kantholz44mm/led_watch/software/src/core/reset.c

extern int main(void);

// Startup code
__attribute__((naked, noreturn)) void _reset(void)
{
    // memset .bss to zero, and copy .data section to RAM region
    extern long _sbss, _ebss, _sdata, _edata, _sidata;
    for (long *dst = &_sbss; dst < &_ebss; dst++) *dst = 0;
    for (long *dst = &_sdata, *src = &_sidata; dst < &_edata;) *dst++ = *src++;

    main();             // Call main()
    for (;;) (void) 0;  // Infinite loop in the case if main() returns
}
